robotlem/Jupiter-project/Hardware/015_Programmier_Modul/Programming_plate.dxf

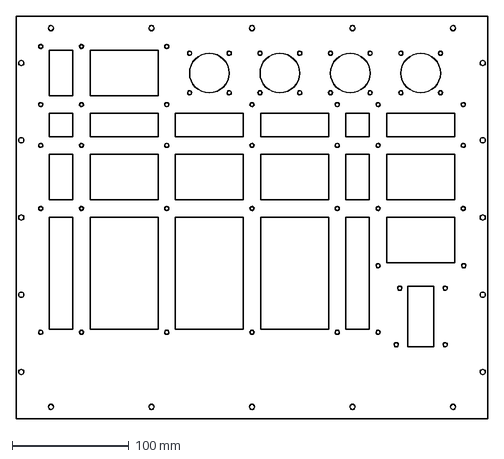
[picture p23: CAD file, 2026-06-11]
Hardware/015_Programmier_Modul/Programming_plate.dxf
405.0 x 345.0 mm
