robotlem/Jupiter-project/Hardware/025_Haptische_Encoder/Motorhalter_v4-KörperPad005.stl

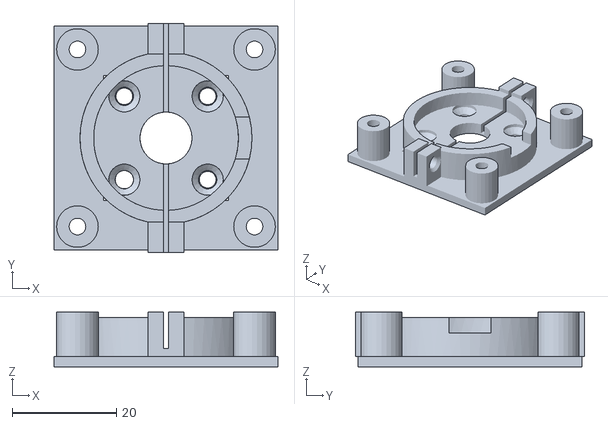
[picture p24: CAD file, 2026-06-11]
Hardware/025_Haptische_Encoder/Motorhalter_v4-KörperPad005.stl
43.0 x 44.0 x 10.5
