robotlem/Jupiter-project/Hardware/100_Sonstiges/Mac_mini_servo_arm.FCStd

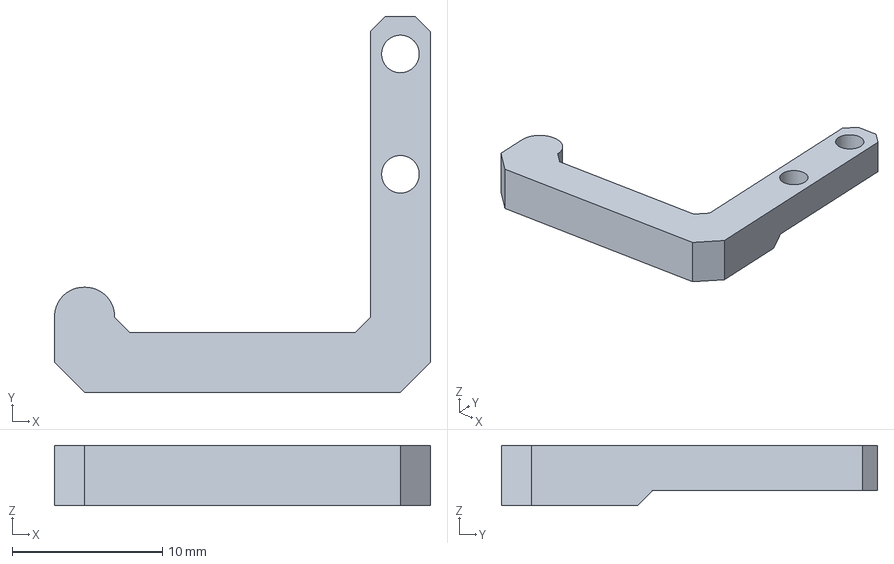
[picture p25: CAD file, 2026-06-11]
Hardware/100_Sonstiges/Mac_mini_servo_arm.FCStd
25.0 x 25.0 x 4.00 mm
