robotlem/Jupiter-project/Hardware/005_Case/Fuerungen/Fuerungen.FCStd

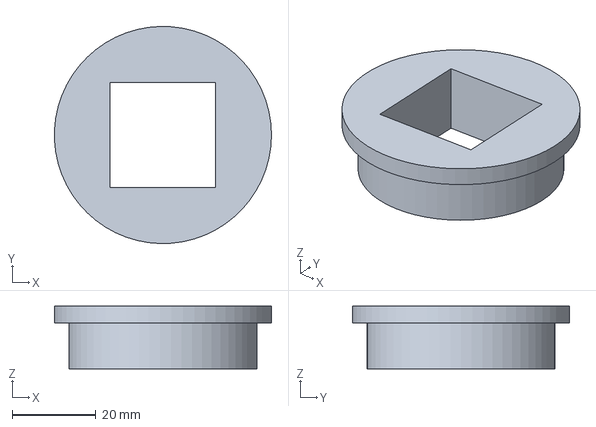
[picture p26: CAD file, 2026-06-11]
Hardware/005_Case/Fuerungen/Fuerungen.FCStd
52.0 x 52.0 x 15.0 mm
