robotlem/Jupiter-project/Hardware/010_Fader_Modul/Mechanical/3D-Druck/Fader_switch_holder_2x6-Körper001.stl

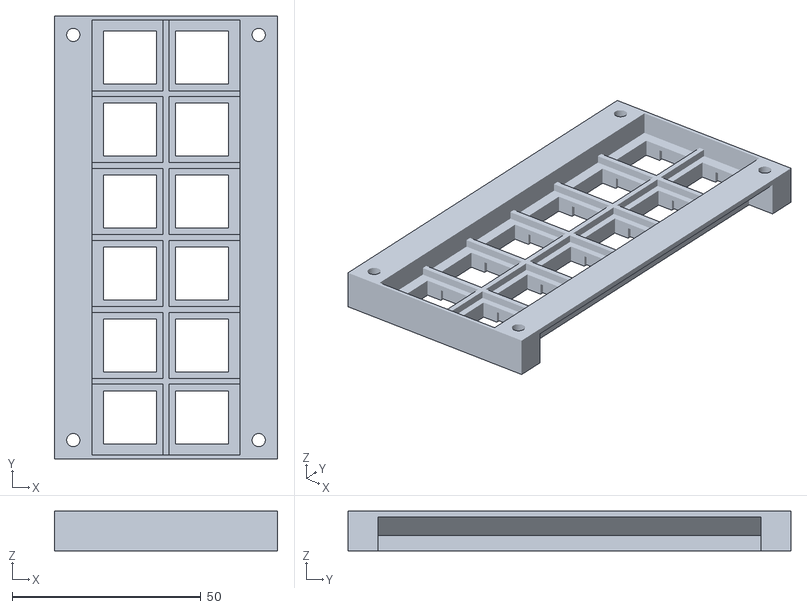
[picture p27: CAD file, 2026-06-11]
Hardware/010_Fader_Modul/Mechanical/3D-Druck/Fader_switch_holder_2x6-Körper001.stl
59.1 x 117.3 x 10.5
