robotlem/Jupiter-project/Hardware/010_Fader_Modul/Mechanical/FaderPlate.dxf

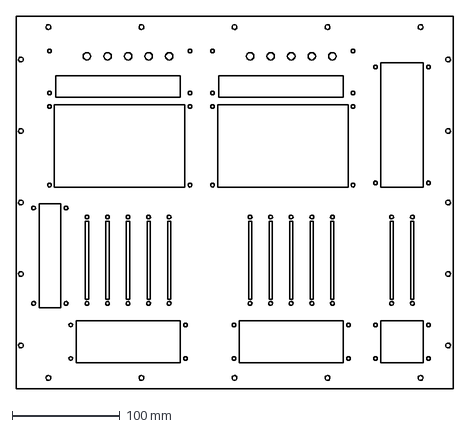
[picture p28: CAD file, 2026-06-11]
Hardware/010_Fader_Modul/Mechanical/FaderPlate.dxf
405.0 x 345.0 mm
