robotlem/Jupiter-project/Hardware/015_Programmier_Modul/Keyswitchholder_0-KörperPocket001.stl

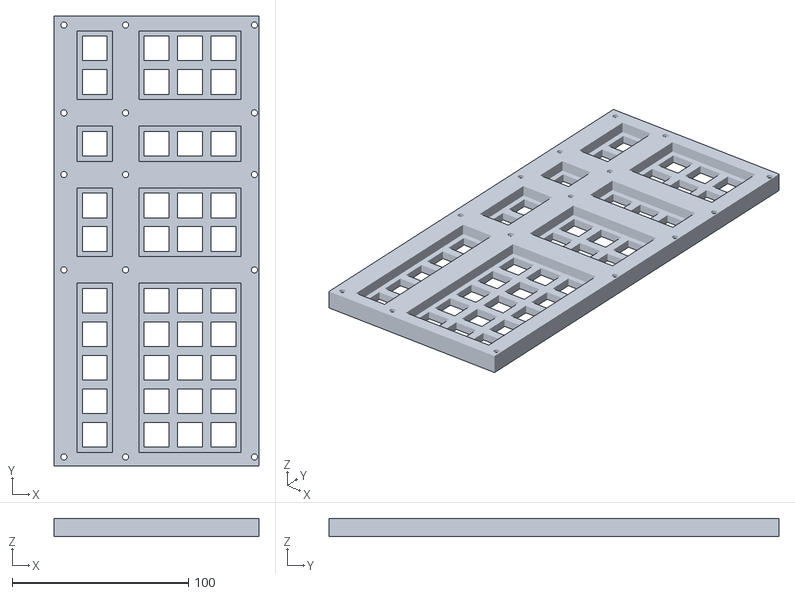
[picture p29: CAD file, 2026-06-11]
Hardware/015_Programmier_Modul/Keyswitchholder_0-KörperPocket001.stl
116.2 x 255.5 x 10.5
