robotlem/Jupiter-project/Hardware/025_Haptische_Encoder/Motorhalter_v2-2-3stk.3mf

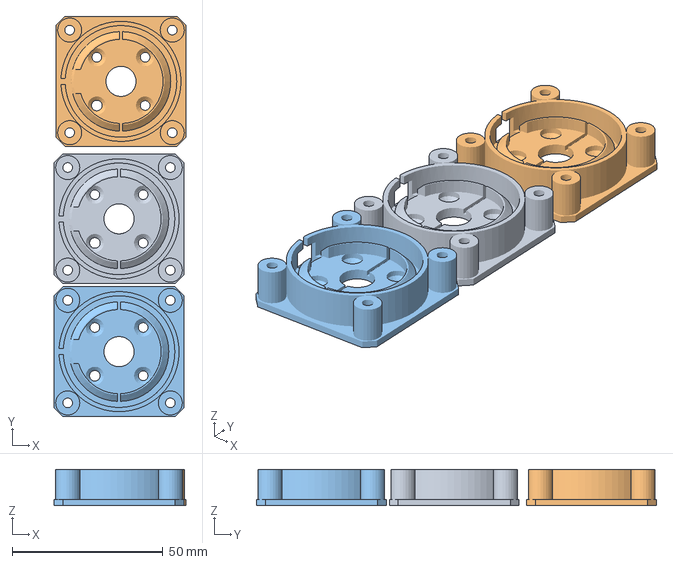
[picture p30: CAD file, 2026-06-11]
Hardware/025_Haptische_Encoder/Motorhalter_v2-2-3stk.3mf
43.6 x 132.6 x 12.0 mm
Motorhalter_v2-2-KörperPocket009.stl x 3
