robotlem/Jupiter-project/Hardware/100_Sonstiges/chain_end.stl

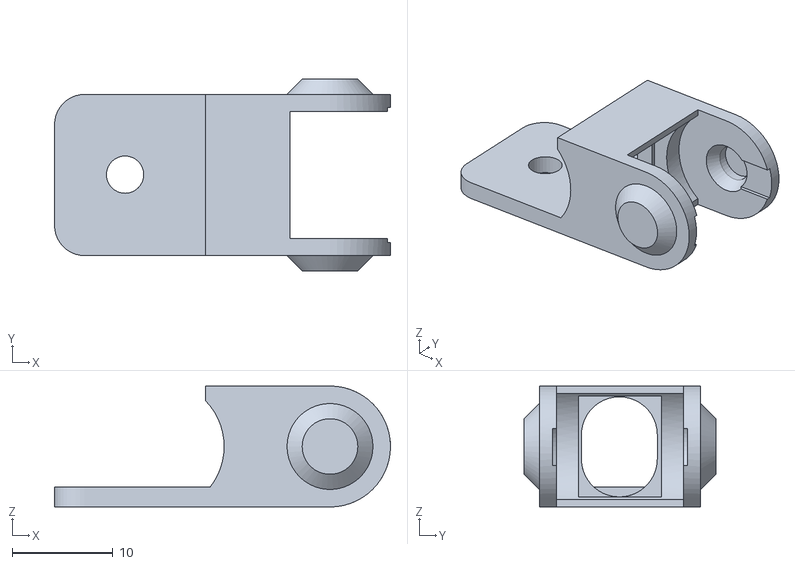
[picture p31: CAD file, 2026-06-11]
Hardware/100_Sonstiges/chain_end.stl
33.3 x 19.0 x 12.0
