robotlem/Jupiter-project/Hardware/010_Fader_Modul/Mechanical/3D-Druck/Fader_switch_holder_1x5-Körper001Chamfer.stl

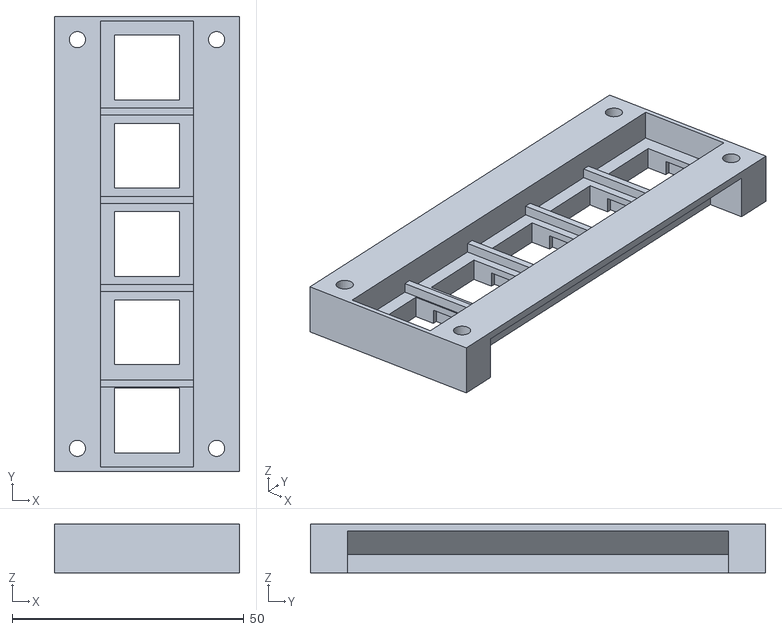
[picture p32: CAD file, 2026-06-11]
Hardware/010_Fader_Modul/Mechanical/3D-Druck/Fader_switch_holder_1x5-Körper001Chamfer.stl
40.0 x 98.2 x 10.5
