robotlem/Jupiter-project/Hardware/010_Fader_Modul/Mechanical/Front_plate_version2_only_holes.FCStd

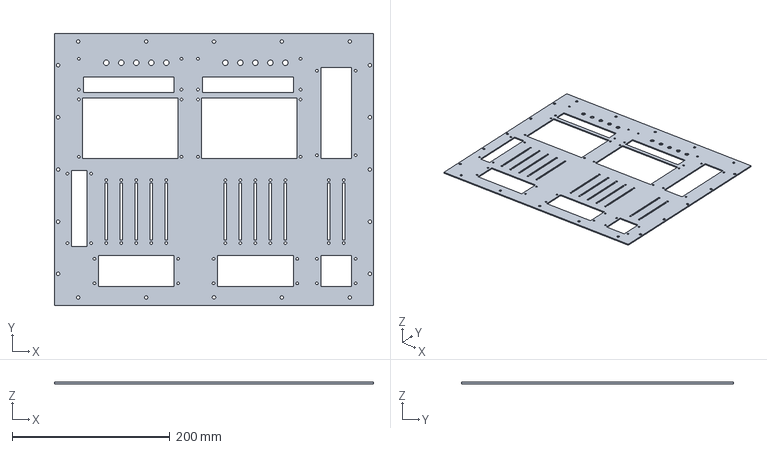
[picture p33: CAD file, 2026-06-11]
Hardware/010_Fader_Modul/Mechanical/Front_plate_version2_only_holes.FCStd
405.0 x 345.0 x 2.00 mm
