robotlem/Jupiter-project/Hardware/015_Programmier_Modul/Keyswitchholder_0.FCStd

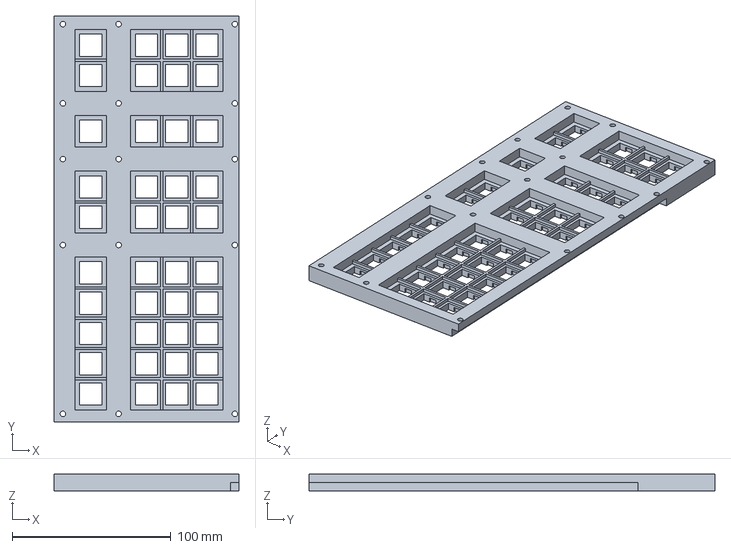
[picture p34: CAD file, 2026-06-11]
Hardware/015_Programmier_Modul/Keyswitchholder_0.FCStd
116.2 x 255.5 x 10.5 mm
