robotlem/Jupiter-project/Hardware/025_Haptische_Encoder/Motorhalter_v2.FCStd

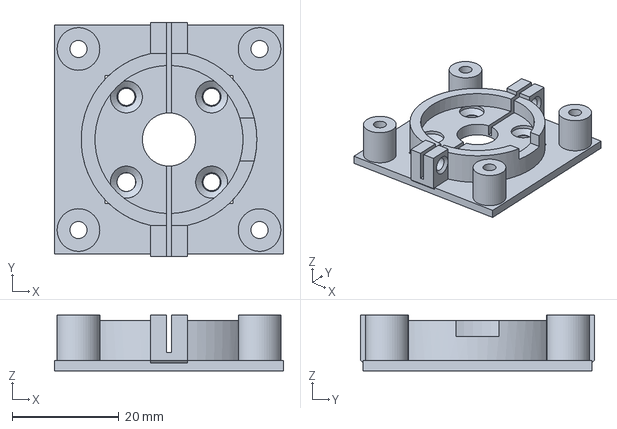
[picture p35: CAD file, 2026-06-11]
Hardware/025_Haptische_Encoder/Motorhalter_v2.FCStd
43.0 x 44.0 x 10.5 mm
