robotlem/Jupiter-project/Hardware/100_Sonstiges/Mac-Mini-Halter.FCStd

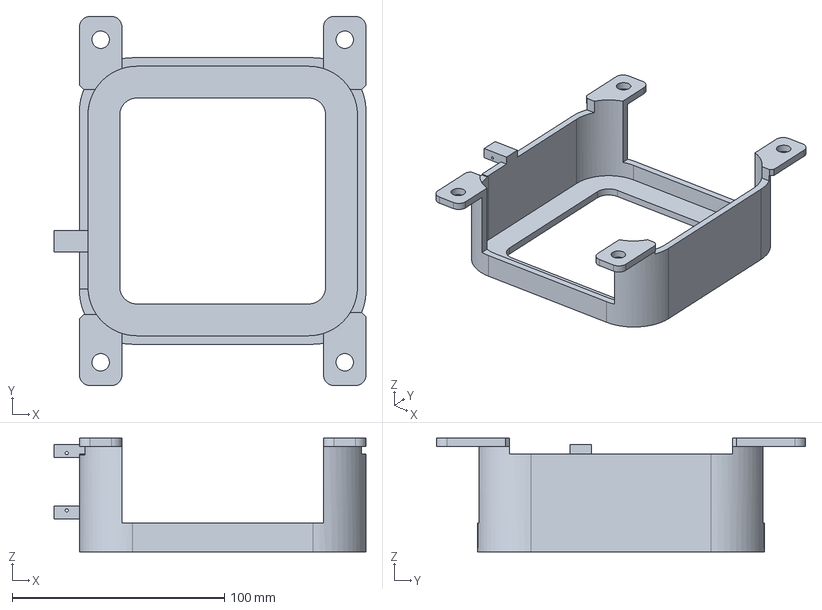
[picture p36: CAD file, 2026-06-11]
Hardware/100_Sonstiges/Mac-Mini-Halter.FCStd
147.0 x 174.0 x 53.5 mm
