robotlem/Jupiter-project/Hardware/005_Case/Fuerungen/Fuerungen_Drehpunkt.stl

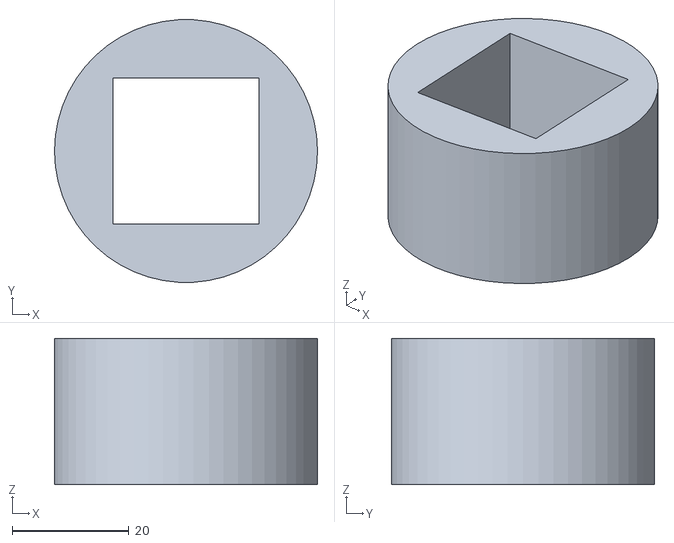
[picture p37: CAD file, 2026-06-11]
Hardware/005_Case/Fuerungen/Fuerungen_Drehpunkt.stl
45.0 x 44.9 x 25.0
