robotlem/Jupiter-project/Hardware/025_Haptische_Encoder/Motorhalter_v2-2-KörperPocket009.stl

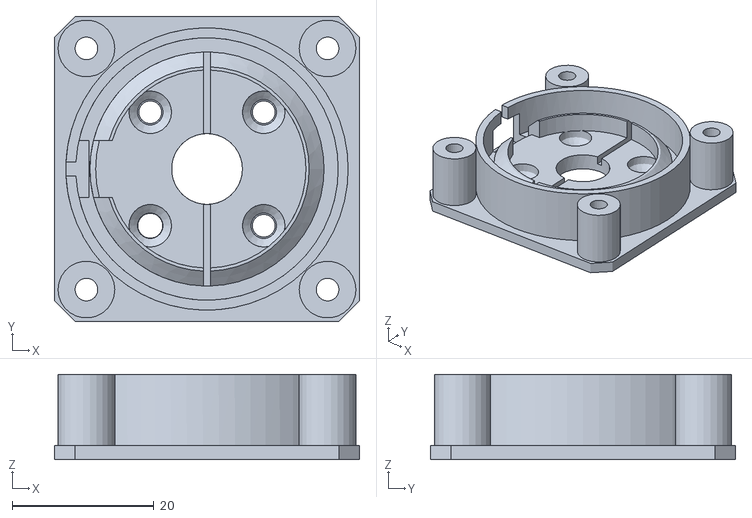
[picture p38: CAD file, 2026-06-11]
Hardware/025_Haptische_Encoder/Motorhalter_v2-2-KörperPocket009.stl
43.0 x 43.0 x 12.0
