robotlem/Jupiter-project/Hardware/100_Sonstiges/chain_start.stl

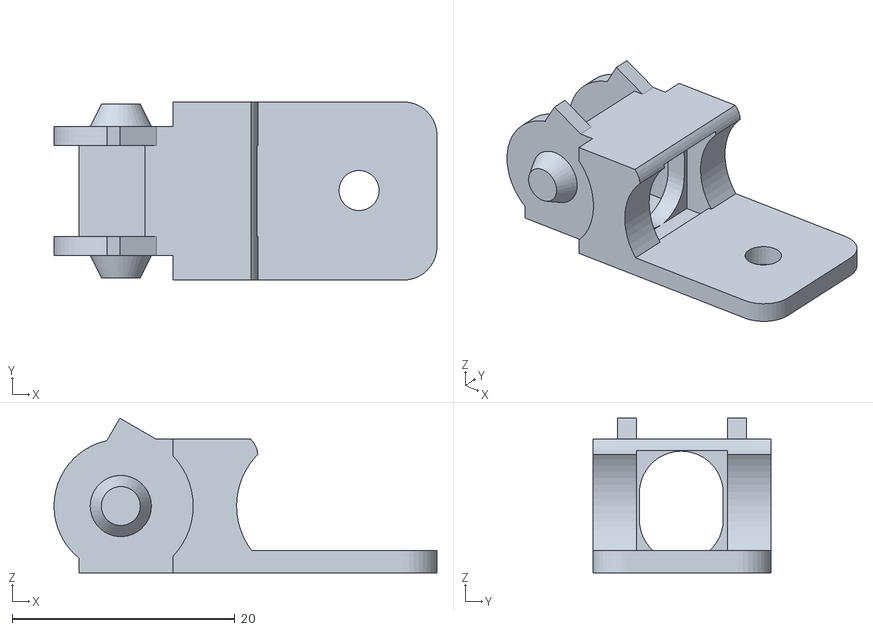
[picture p39: CAD file, 2026-06-11]
Hardware/100_Sonstiges/chain_start.stl
34.4 x 16.0 x 13.9
