robotlem/Jupiter-project/Hardware/005_Case/Fuerungen/Fuerung_Klein.stl

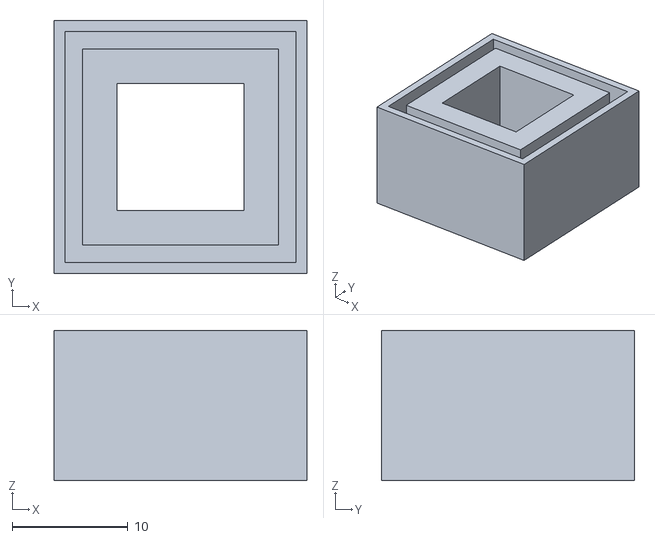
[picture p40: CAD file, 2026-06-11]
Hardware/005_Case/Fuerungen/Fuerung_Klein.stl
21.9 x 21.9 x 13.0
