robotlem/Jupiter-project/Hardware/005_Case/Fuerungen/Fuerung_Gross.stl

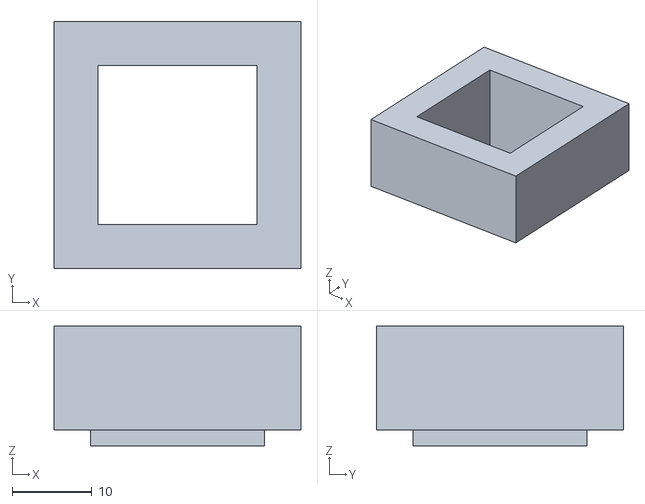
[picture p42: CAD file, 2026-06-11]
Hardware/005_Case/Fuerungen/Fuerung_Gross.stl
31.0 x 31.0 x 15.0
