robotlem/Jupiter-project/Hardware/010_Fader_Modul/Mechanical/3D-Druck/Fader_switch_holder.FCStd

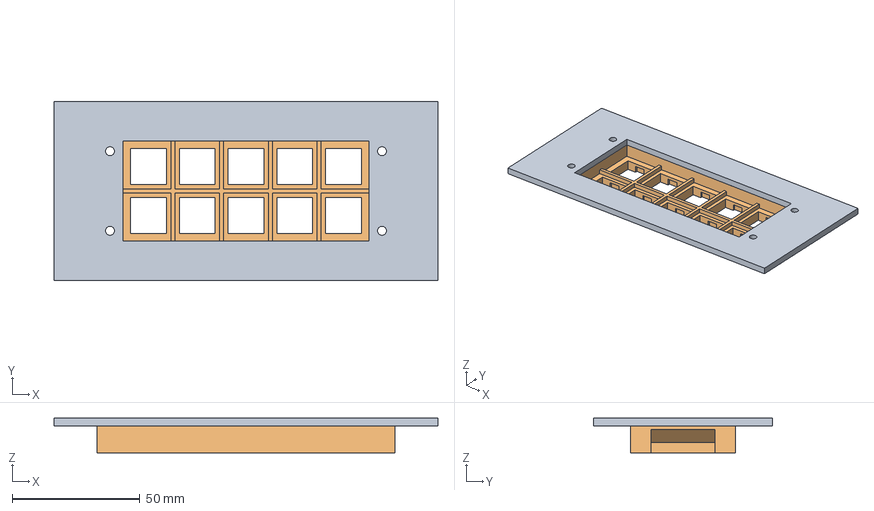
[picture p43: CAD file, 2026-06-11]
Hardware/010_Fader_Modul/Mechanical/3D-Druck/Fader_switch_holder.FCStd
150.0 x 70.0 x 13.5 mm
Frontplate
Körper001
