robotlem/Jupiter-project/Hardware/025_Haptische_Encoder/Motorhalter.FCStd

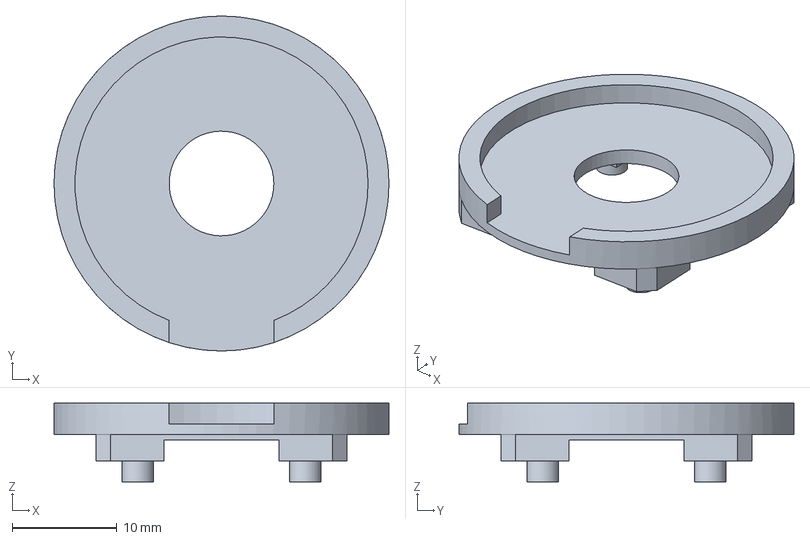
[picture p44: CAD file, 2026-06-11]
Hardware/025_Haptische_Encoder/Motorhalter.FCStd
32.0 x 32.0 x 7.50 mm
