robotlem/Jupiter-project/Hardware/010_Fader_Modul/Mechanical/3D-Druck/Fader_switch_holder_2x2-Körper001Chamfer.stl

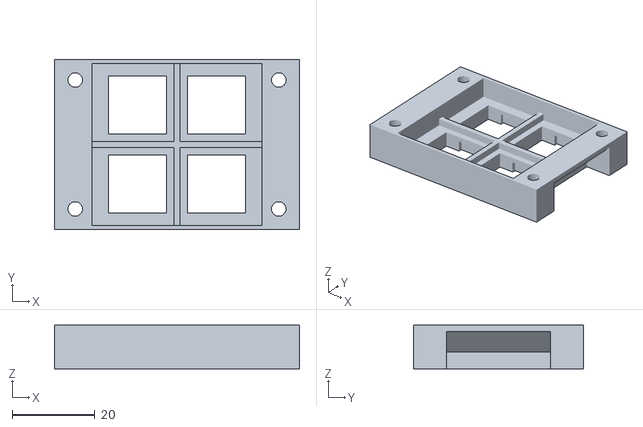
[picture p45: CAD file, 2026-06-11]
Hardware/010_Fader_Modul/Mechanical/3D-Druck/Fader_switch_holder_2x2-Körper001Chamfer.stl
59.1 x 41.1 x 10.5
