robotlem/Jupiter-project/Hardware/010_Fader_Modul/Mechanical/3D-Druck/Fader_switch_holder_2x6.FCStd

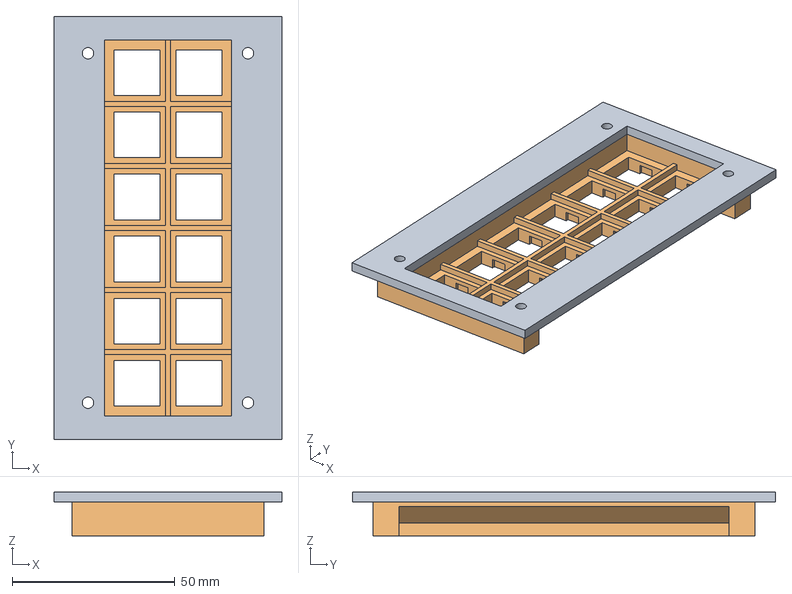
[picture p46: CAD file, 2026-06-11]
Hardware/010_Fader_Modul/Mechanical/3D-Druck/Fader_switch_holder_2x6.FCStd
70.0 x 130.0 x 13.5 mm
Körper
Körper001
